makerphones/first-chair/design/form/profile-study/_contact-iso.png

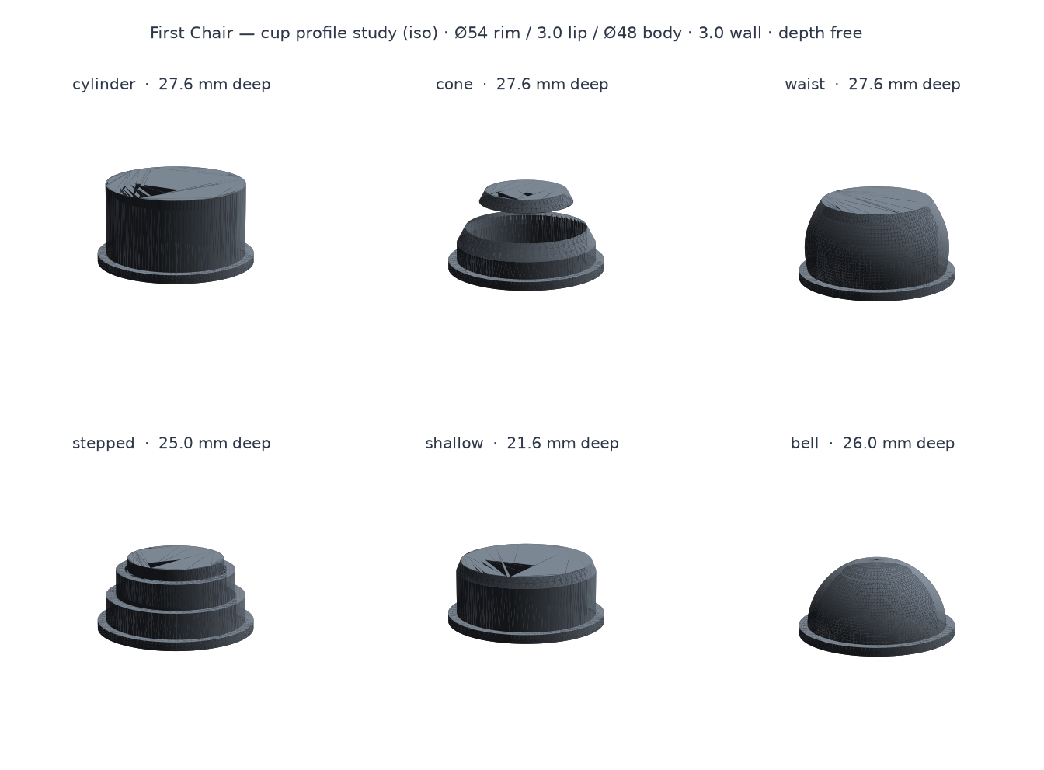
design/form/profile-study/_contact-iso.png
