makerphones/first-chair/design/form/profile-study/_contact-section.png

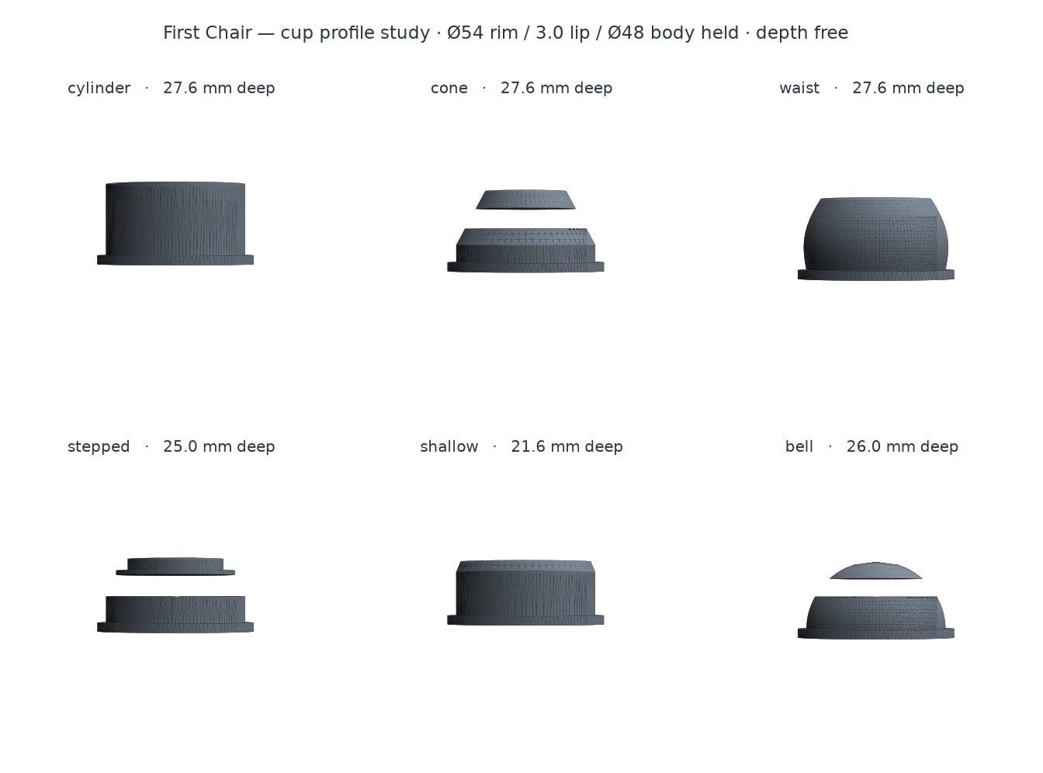
design/form/profile-study/_contact-section.png
