makerphones/first-chair/design/form/profile-study/_contact-side.png

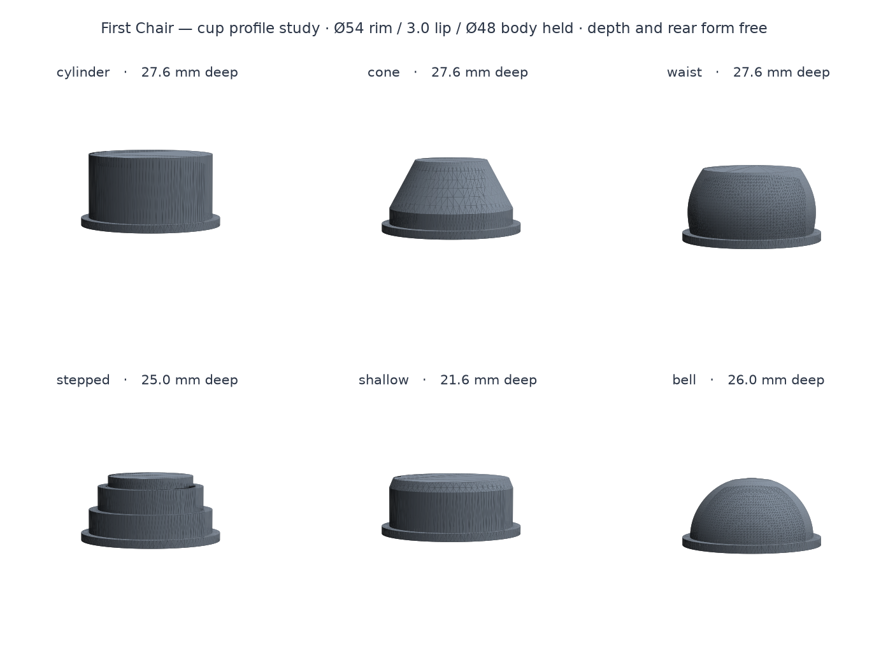
design/form/profile-study/_contact-side.png
