makerphones/first-chair/design/form/profile-study/_contact-splits.png

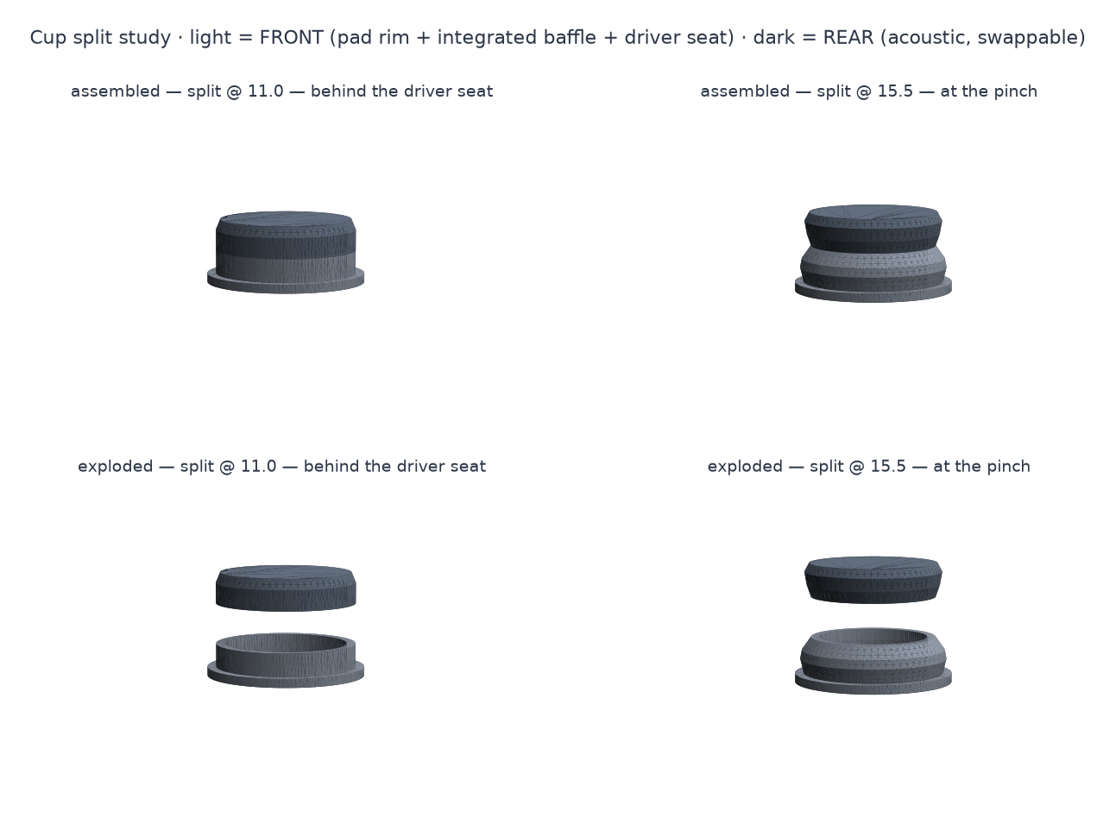
design/form/profile-study/_contact-splits.png
