makerphones/first-chair/design/form/profile-study/_contact-taper.png

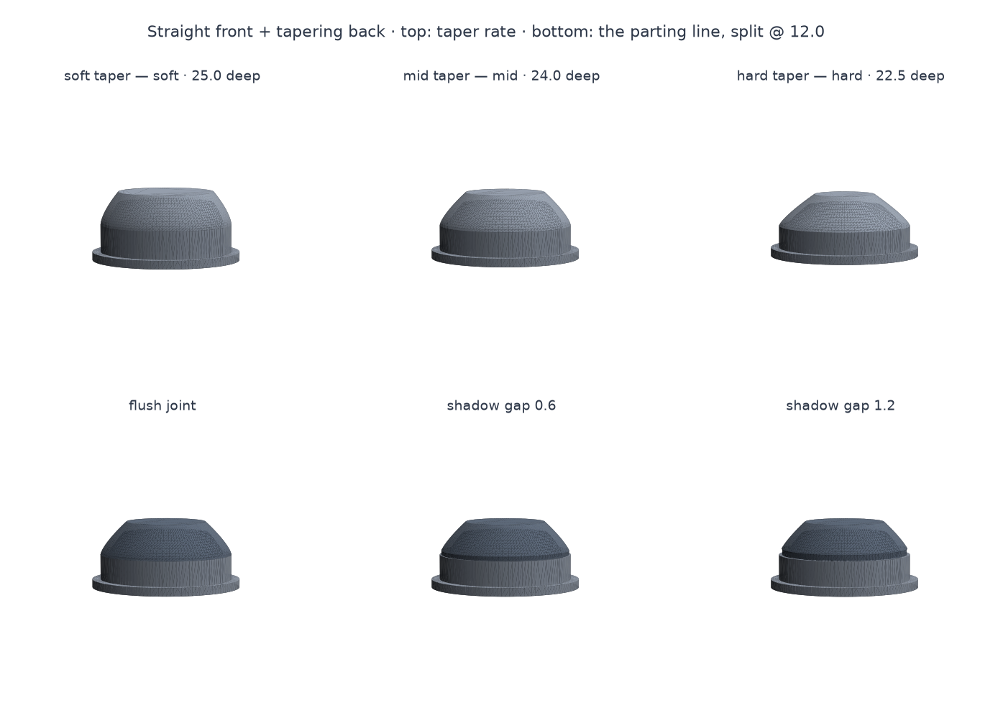
design/form/profile-study/_contact-taper.png
