makerphones/first-chair/design/form/reference/bow-blanks-cut-and-formed.jpg

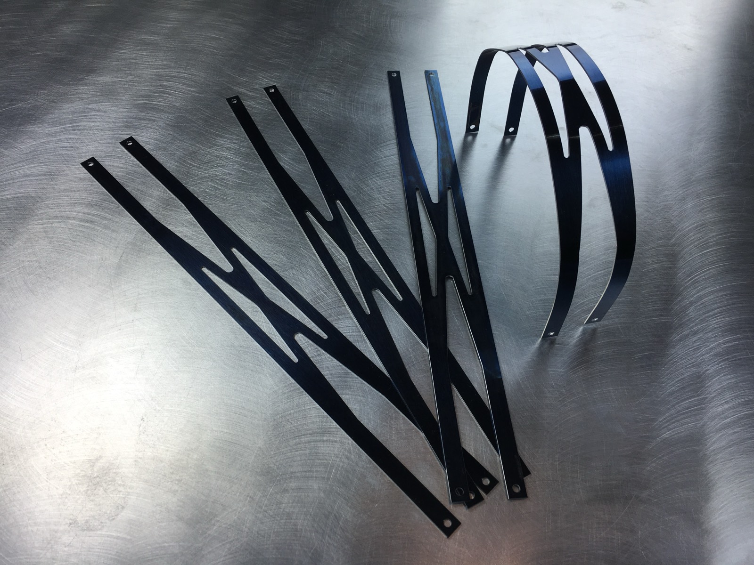
design/form/reference/bow-blanks-cut-and-formed.jpg
