makerphones/first-chair/design/form/reference/dev-6333.jpg

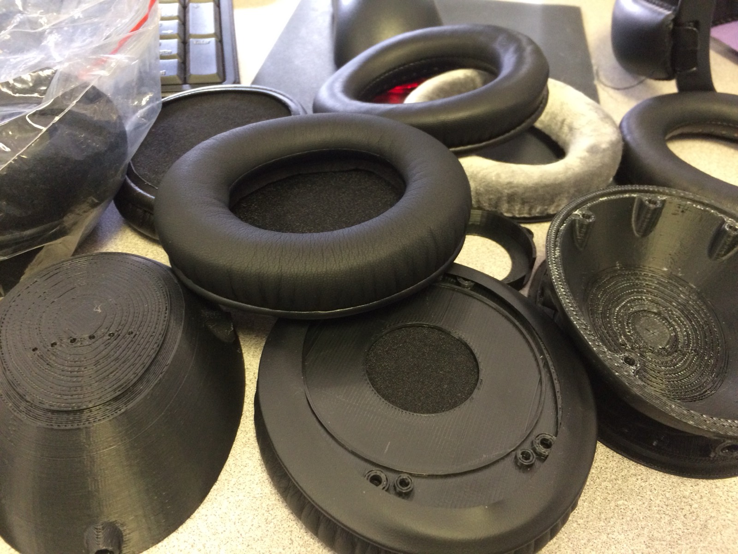
design/form/reference/dev-6333.jpg
