makerphones/first-chair/design/form/reference/dev-6397.jpg

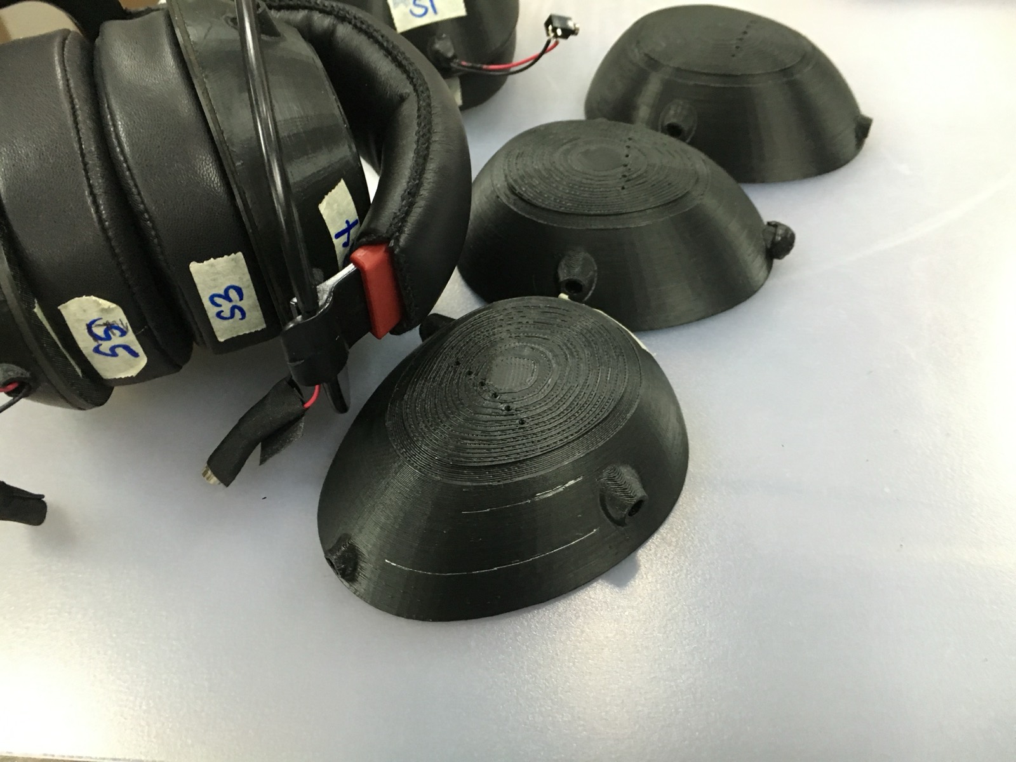
design/form/reference/dev-6397.jpg
