makerphones/first-chair/design/form/reference/dev-6399.jpg

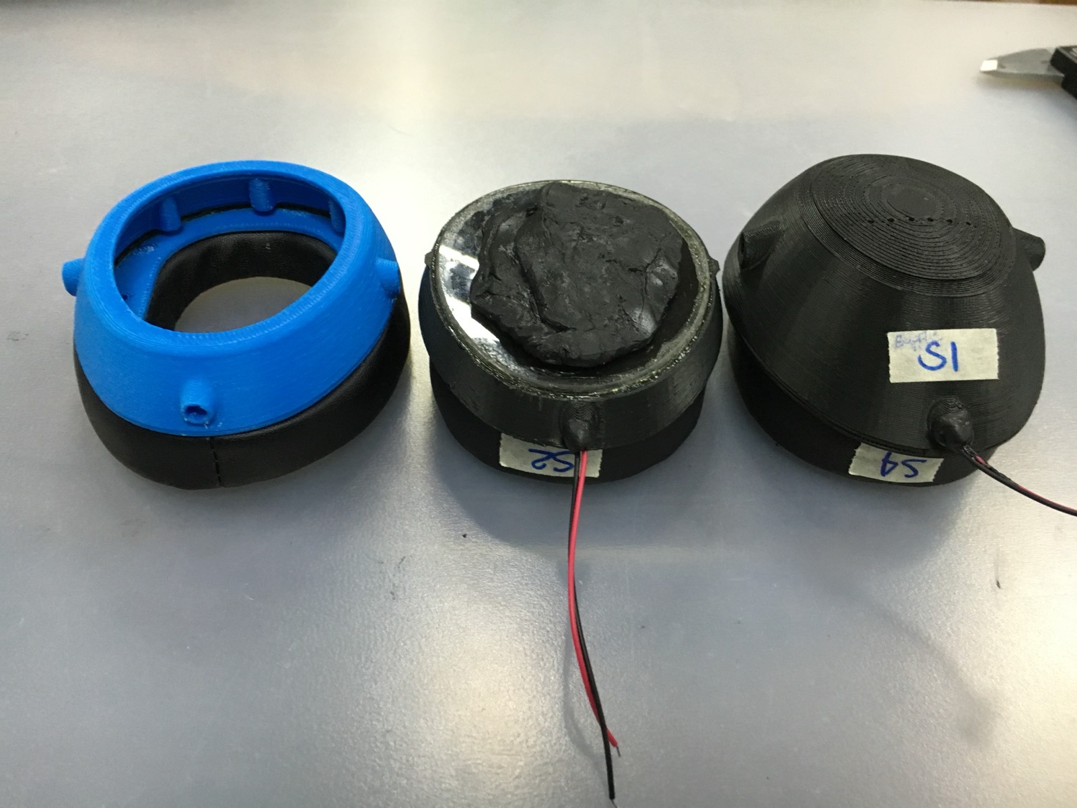
design/form/reference/dev-6399.jpg
