makerphones/first-chair/design/form/reference/dev-6400.jpg

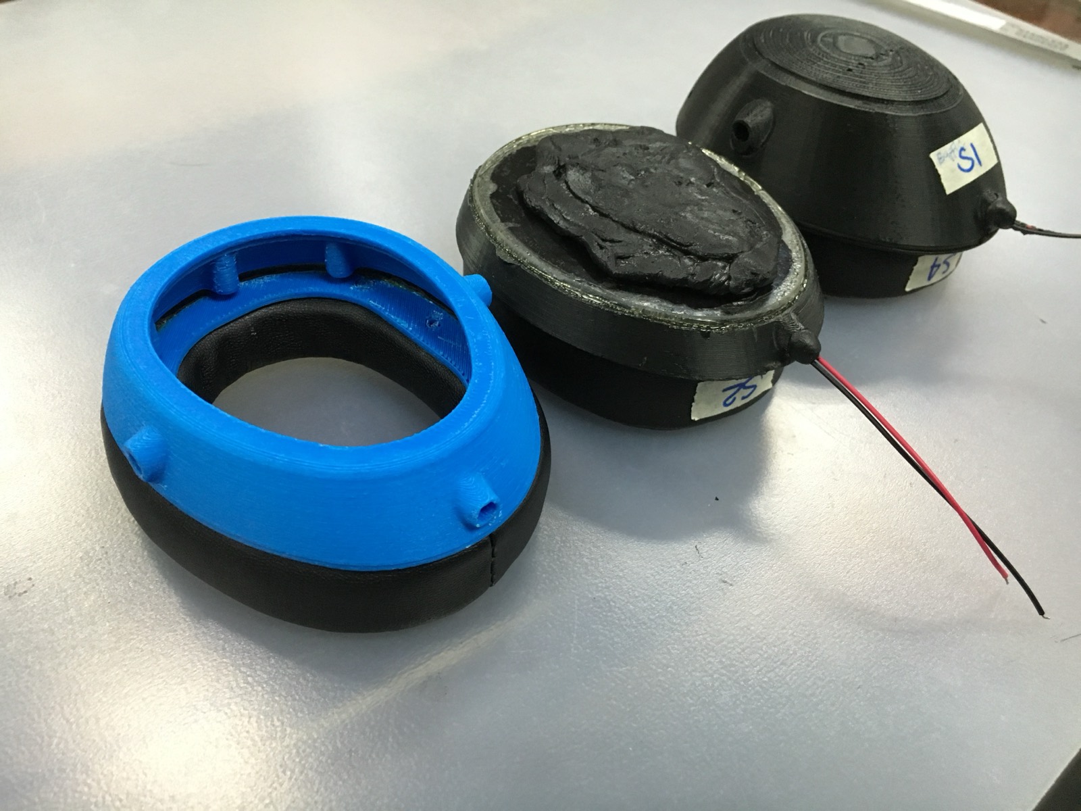
design/form/reference/dev-6400.jpg
