makerphones/first-chair/design/form/reference/dev-6451.jpg

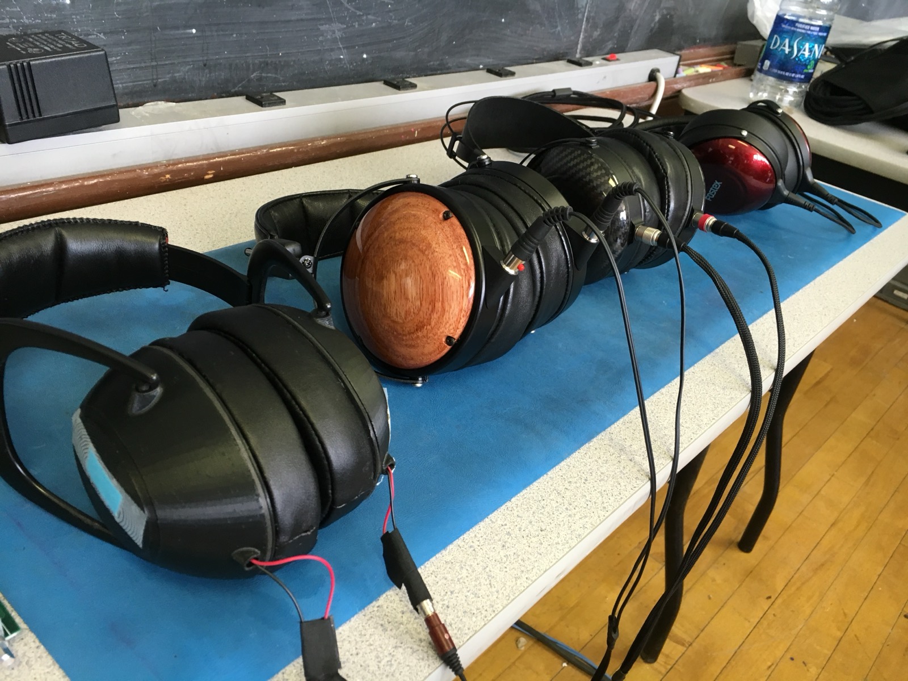
design/form/reference/dev-6451.jpg
