makerphones/first-chair/design/form/reference/dev-7143.jpg

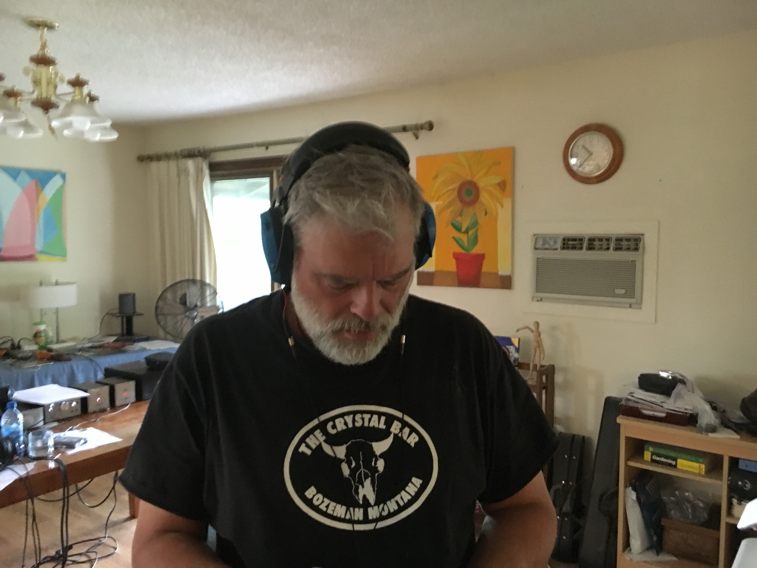
design/form/reference/dev-7143.jpg
