makerphones/first-chair/design/form/reference/dev-7144.jpg

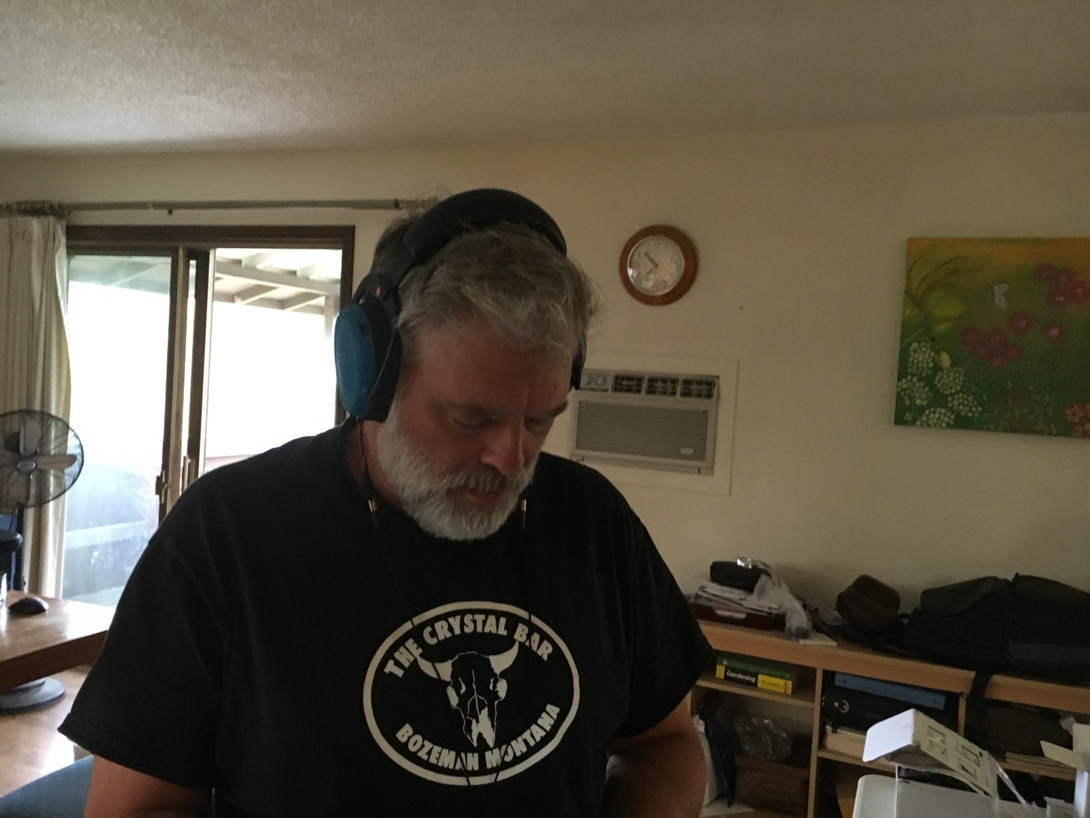
design/form/reference/dev-7144.jpg
