makerphones/first-chair/design/form/reference/driver-70mm-planar.jpg

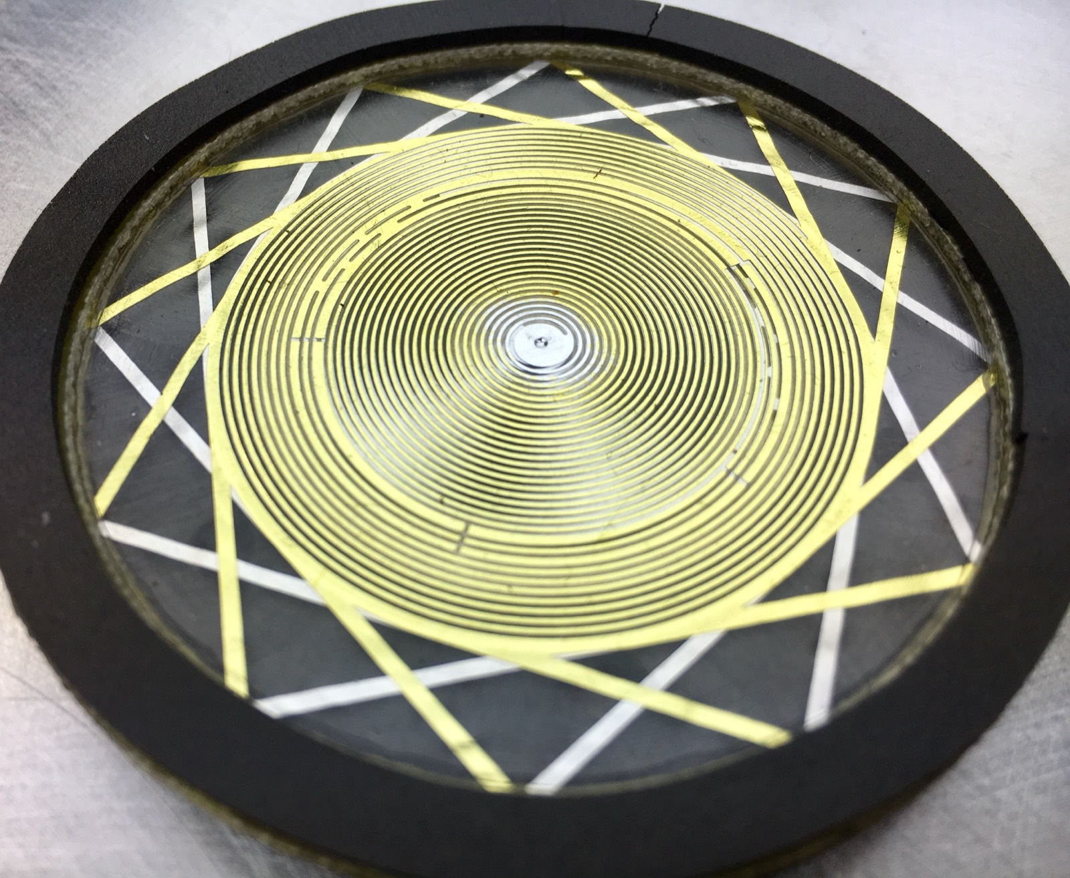
design/form/reference/driver-70mm-planar.jpg
