makerphones/first-chair/design/form/reference/shape-sketch-1a.jpg

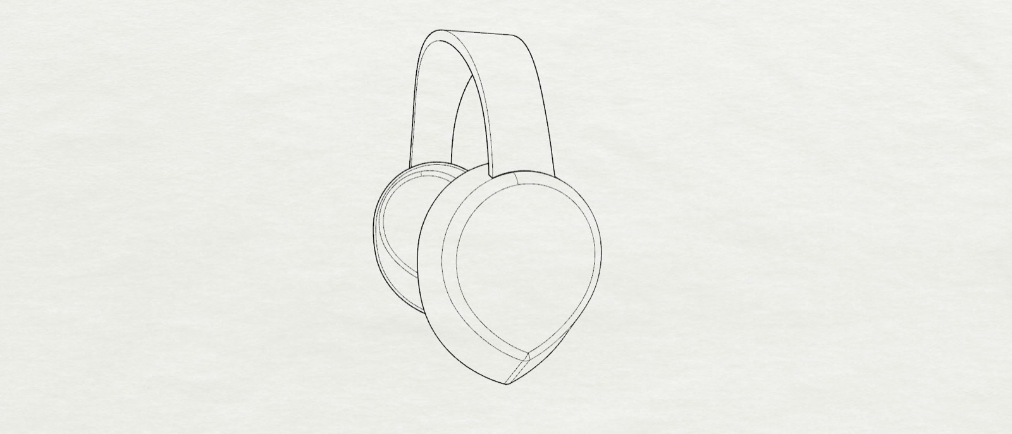
design/form/reference/shape-sketch-1a.jpg
