makerphones/first-chair/design/form/reference/shape-sketch-4a.jpg

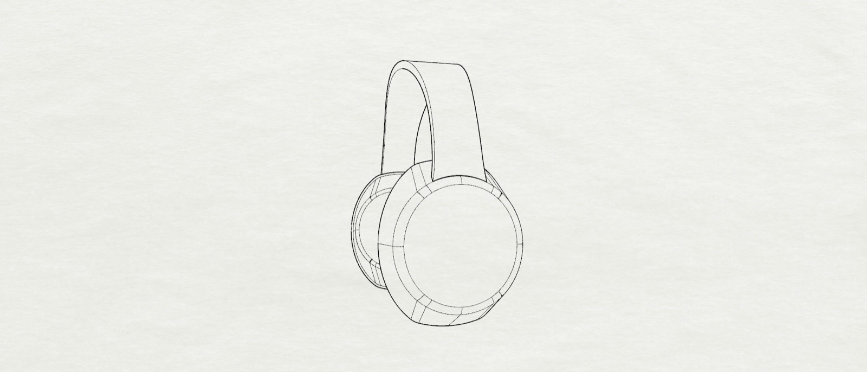
design/form/reference/shape-sketch-4a.jpg
