makerphones/first-chair/design/form/reference/shape-sketches-overview.jpg

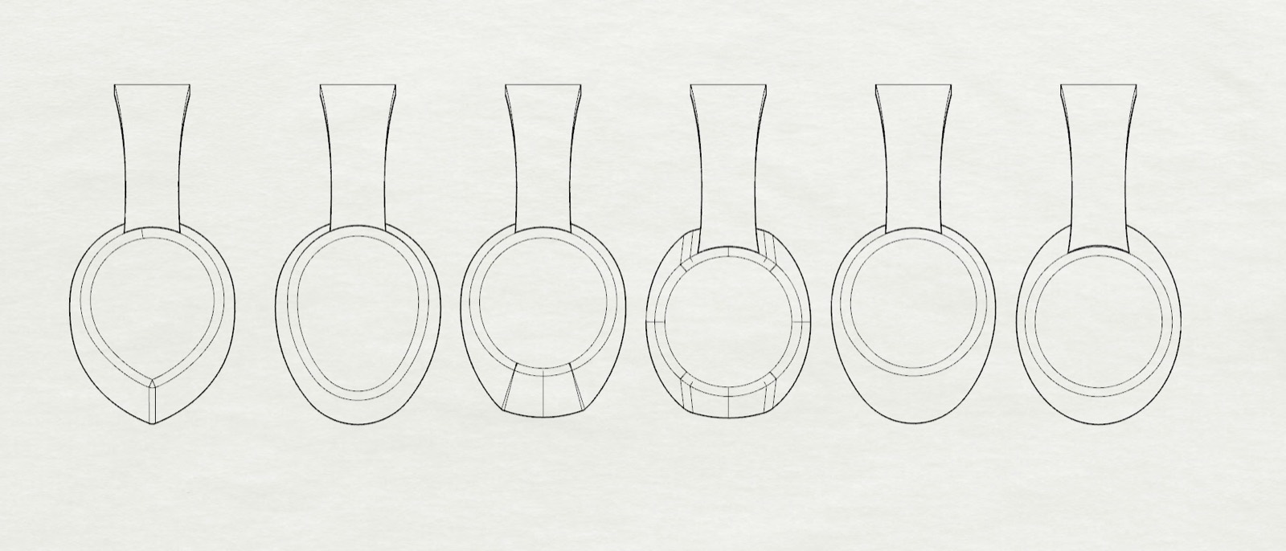
design/form/reference/shape-sketches-overview.jpg
