makerphones/first-chair/docs/renders/adapter_ring_front.png

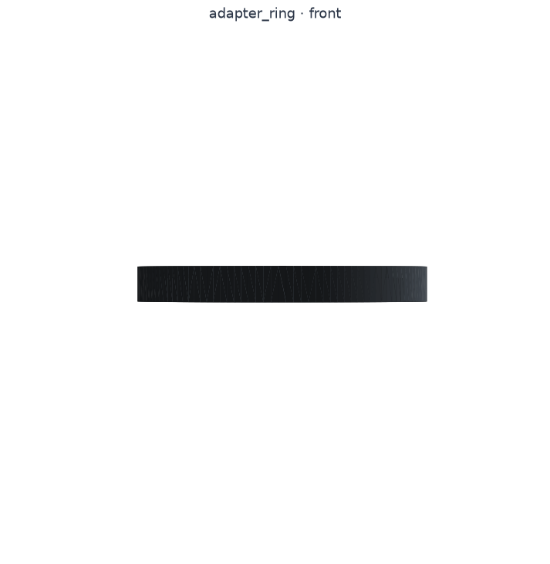
docs/renders/adapter_ring_front.png
