makerphones/first-chair/docs/renders/adapter_ring_iso.png

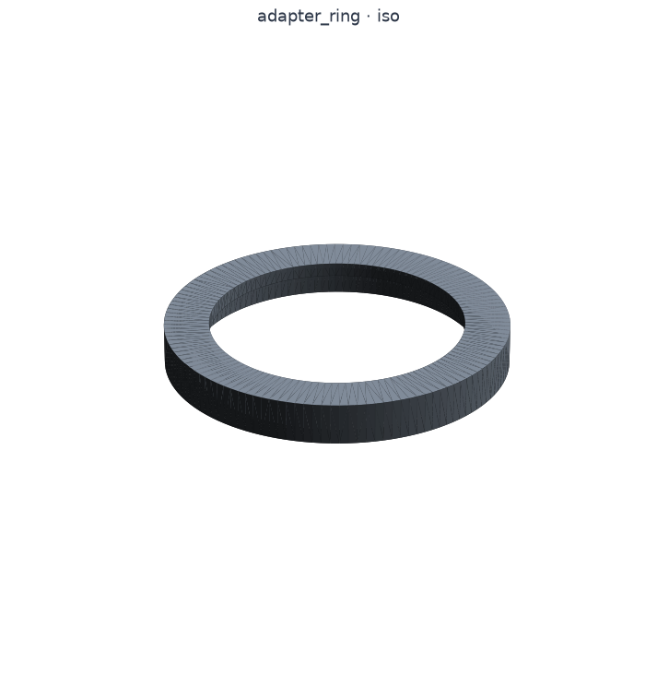
docs/renders/adapter_ring_iso.png
