makerphones/first-chair/docs/renders/cup_iso.png

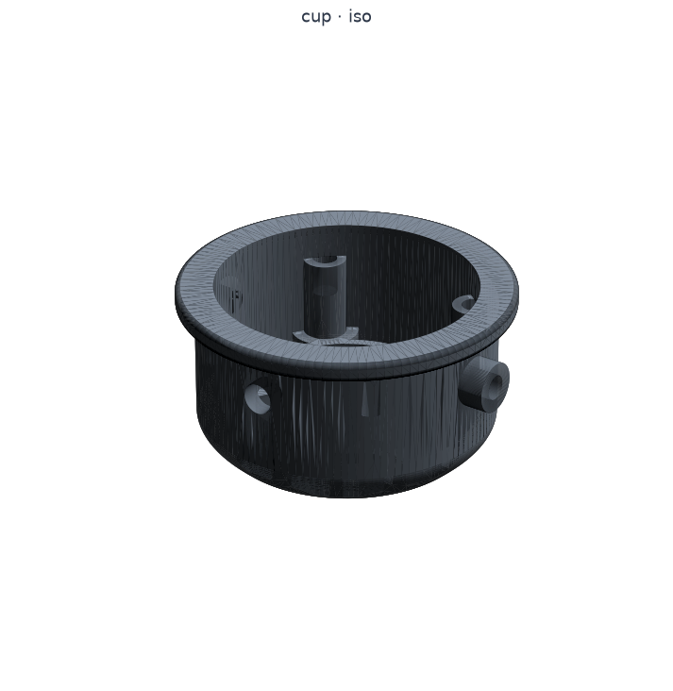
docs/renders/cup_iso.png
