makerphones/first-chair/docs/renders/cup_side.png

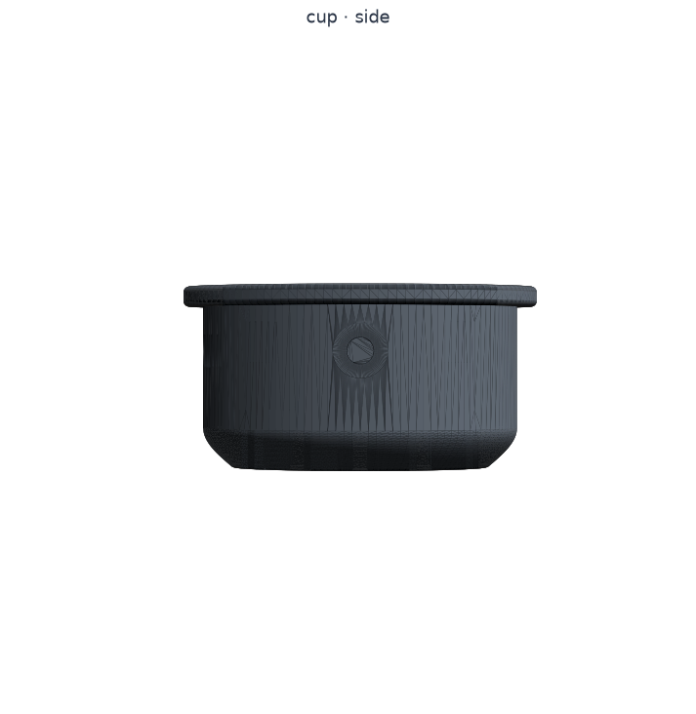
docs/renders/cup_side.png
