makerphones/first-chair/docs/renders/headband_clamp_iso.png

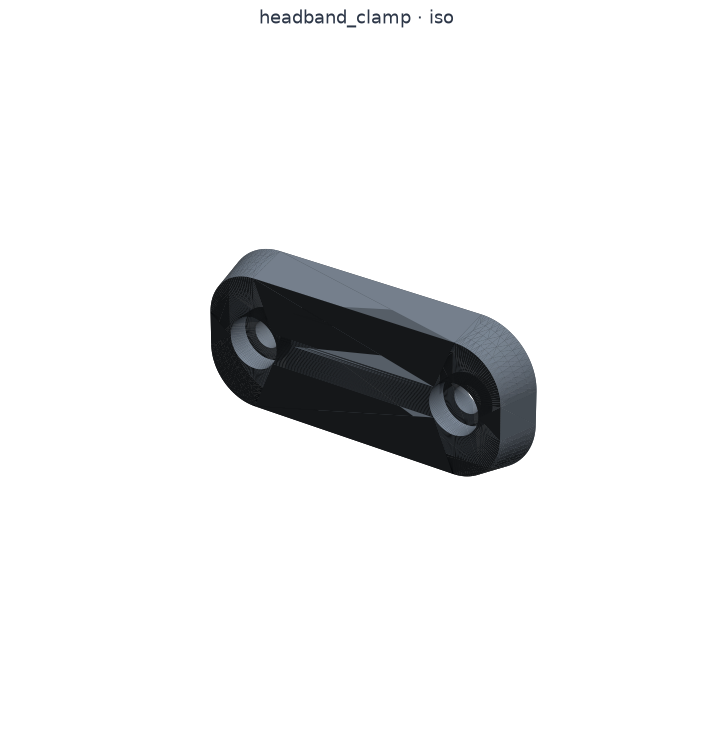
docs/renders/headband_clamp_iso.png
