makerphones/first-chair/docs/renders/headband_clamp_side.png

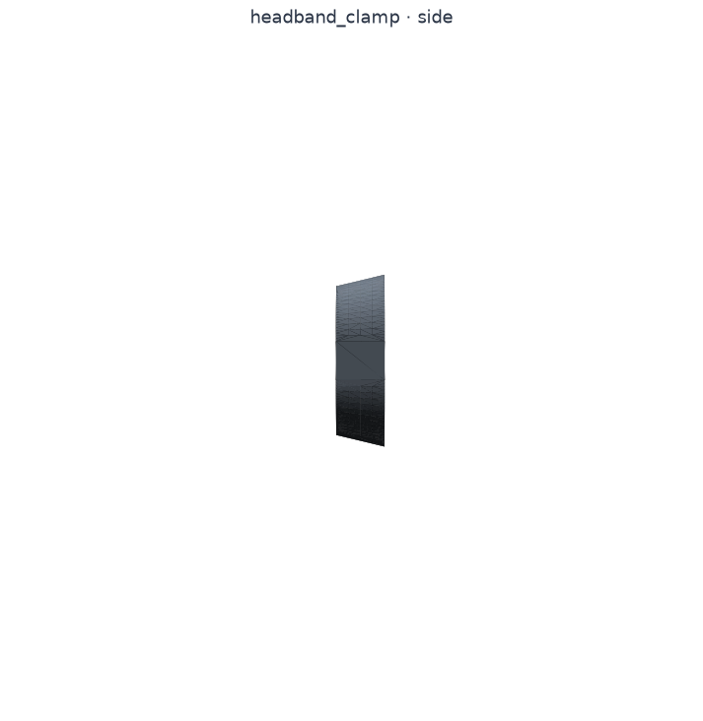
docs/renders/headband_clamp_side.png
