makerphones/first-chair/docs/renders/headband_pad_front.png

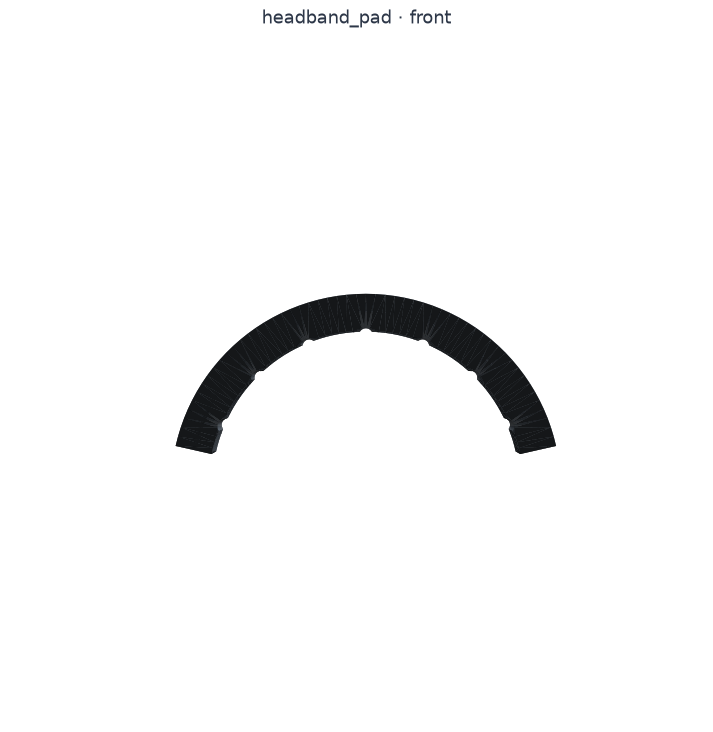
docs/renders/headband_pad_front.png
