makerphones/first-chair/docs/renders/headband_pad_iso.png

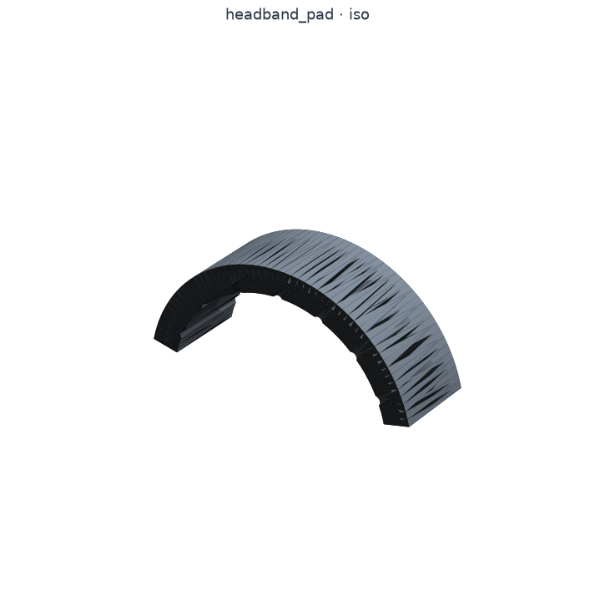
docs/renders/headband_pad_iso.png
