makerphones/first-chair/docs/renders/slider_front.png

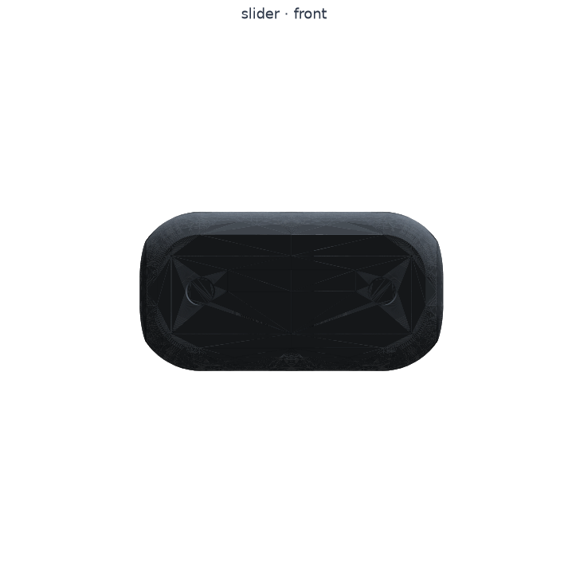
docs/renders/slider_front.png
