makerphones/first-chair/docs/renders/slider_shoe_front.png

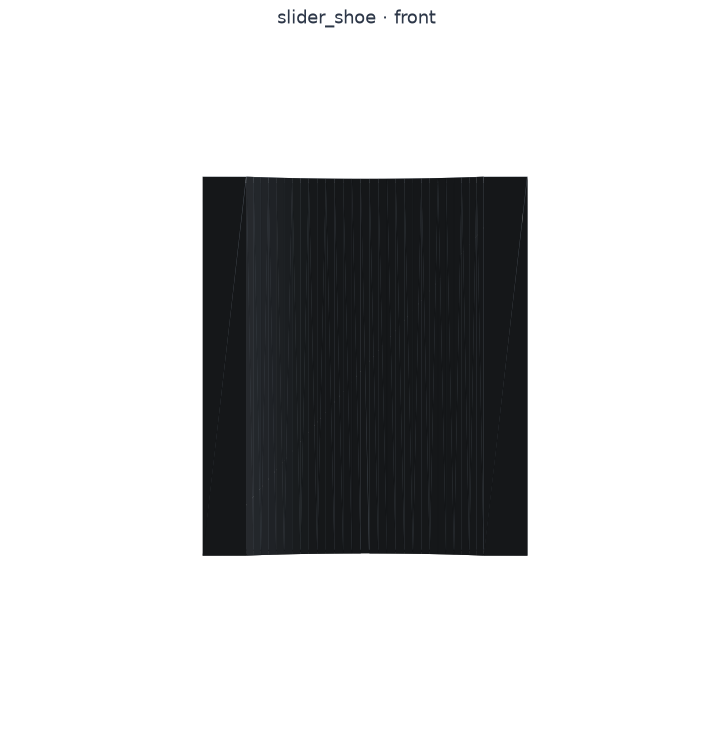
docs/renders/slider_shoe_front.png
