makerphones/first-chair/docs/renders/slider_shoe_iso.png

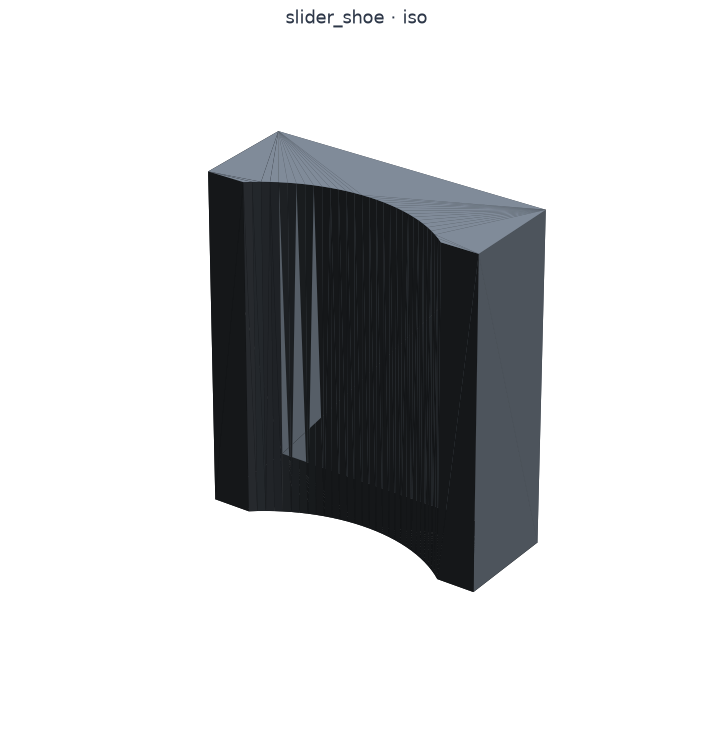
docs/renders/slider_shoe_iso.png
