makerphones/first-chair/docs/renders/slider_shoe_side.png

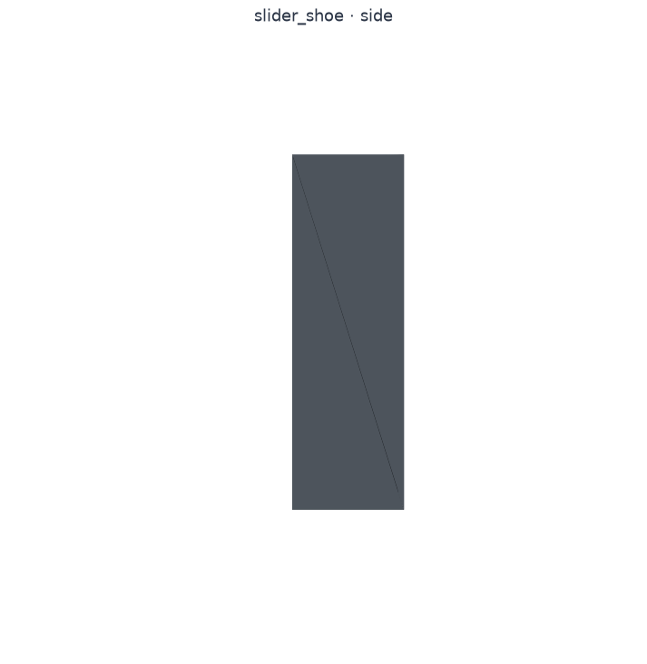
docs/renders/slider_shoe_side.png
