makerphones/first-chair/docs/renders/yoke_front.png

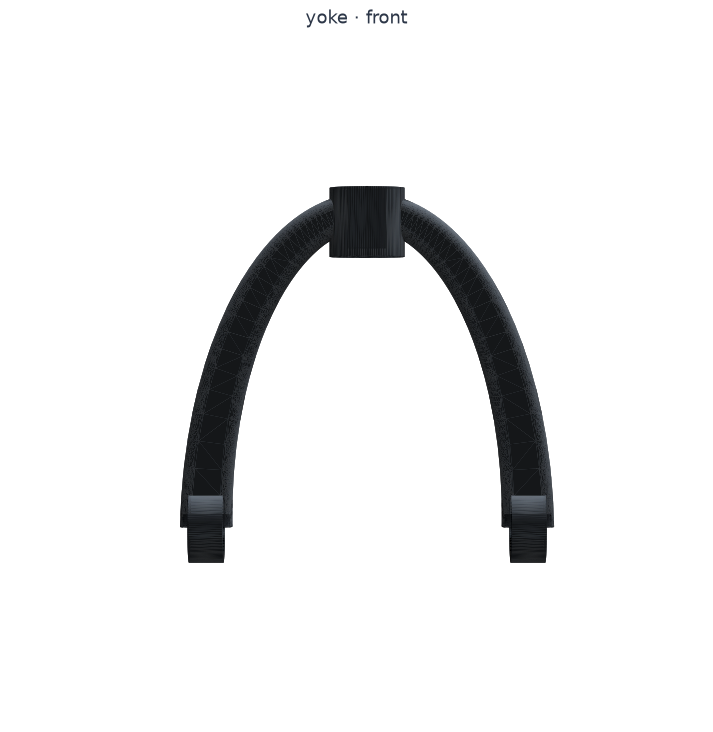
docs/renders/yoke_front.png
