makerphones/first-chair/docs/renders/yoke_iso.png

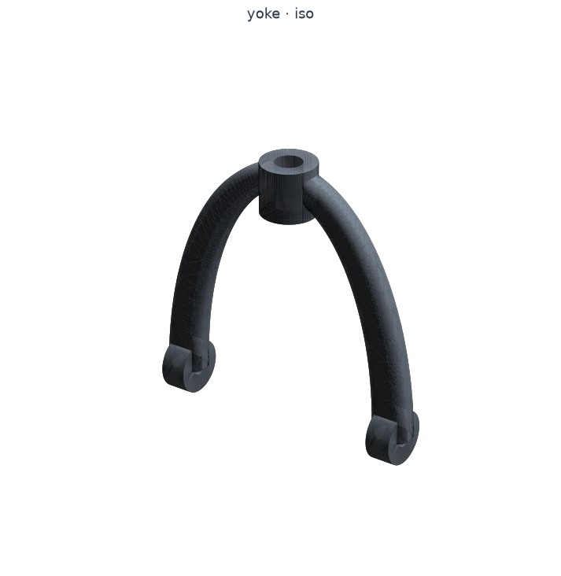
docs/renders/yoke_iso.png
