makerphones/first-chair/docs/renders/yoke_side.png

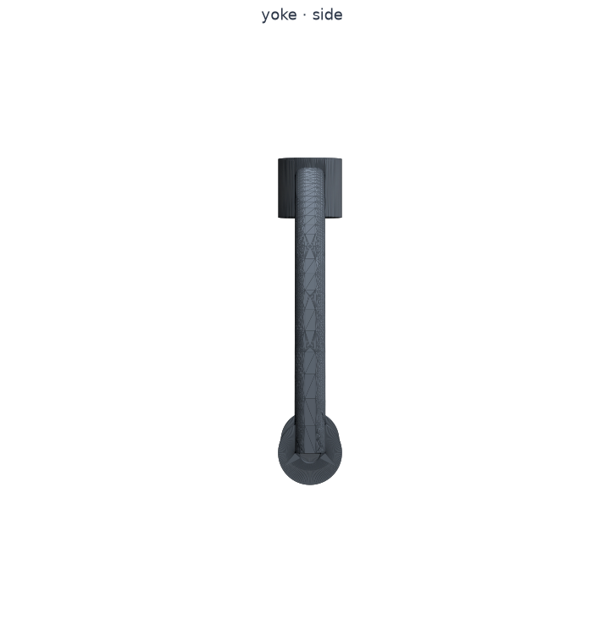
docs/renders/yoke_side.png
