makerphones/first-chair/design/form/profile-study/cone.stl

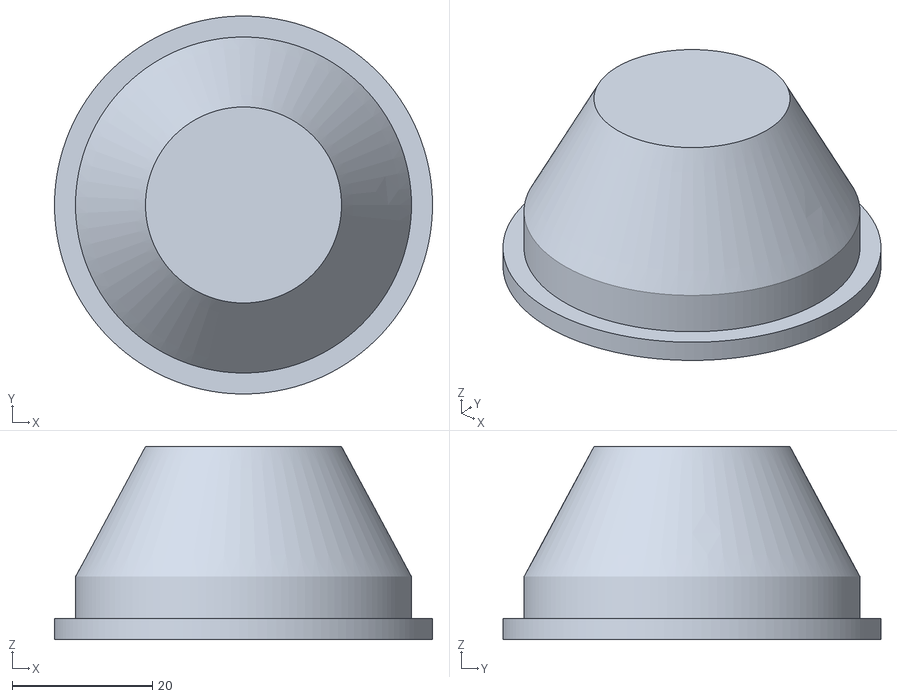
[picture p52: CAD file, 2026-08-07]
design/form/profile-study/cone.stl
54.0 x 54.0 x 27.6
