makerphones/first-chair/design/form/profile-study/waist.stl

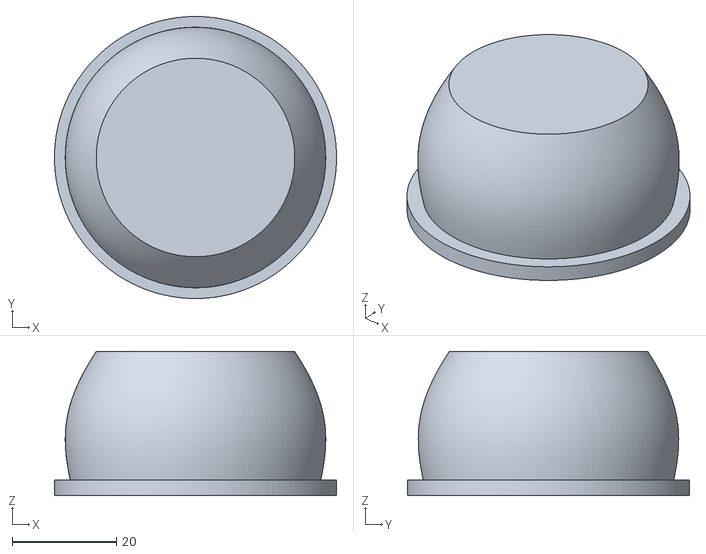
[picture p53: CAD file, 2026-08-07]
design/form/profile-study/waist.stl
54.0 x 54.0 x 27.6
