makerphones/first-chair/design/form/profile-study/shallow.stl

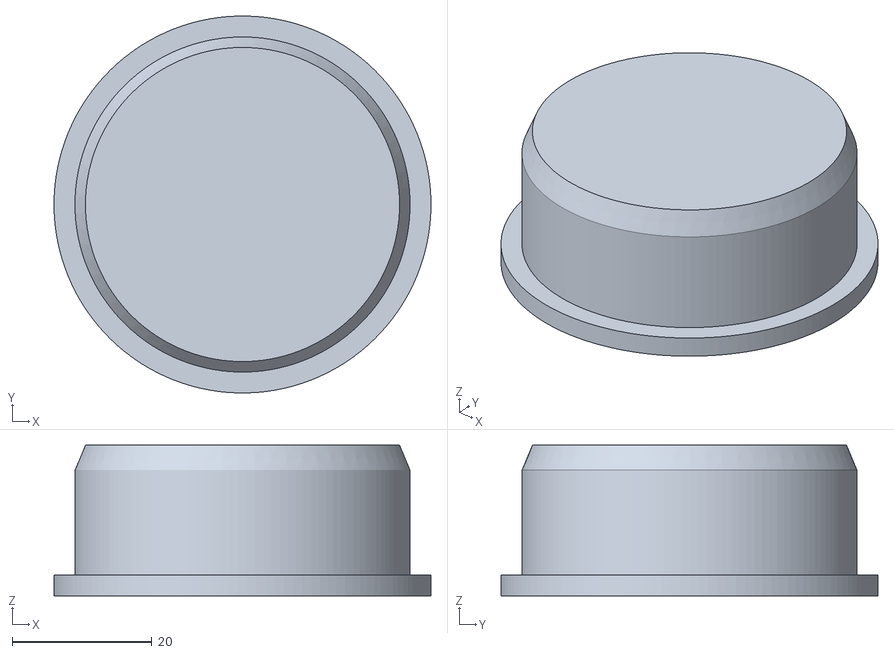
[picture p54: CAD file, 2026-08-07]
design/form/profile-study/shallow.stl
54.0 x 54.0 x 21.6
